Matthias-Stefan/clockgusto/construction/printing/connector_b.stl

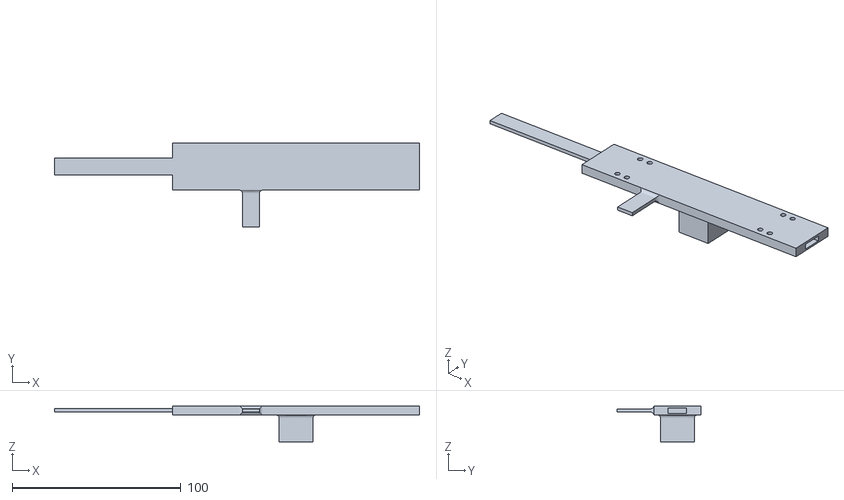
[picture p15: CAD file, 2025-01-12]
construction/printing/connector_b.stl
216.5 x 49.9 x 21.3
