Matthias-Stefan/clockgusto/construction/printing/antenna_nupsi.stl

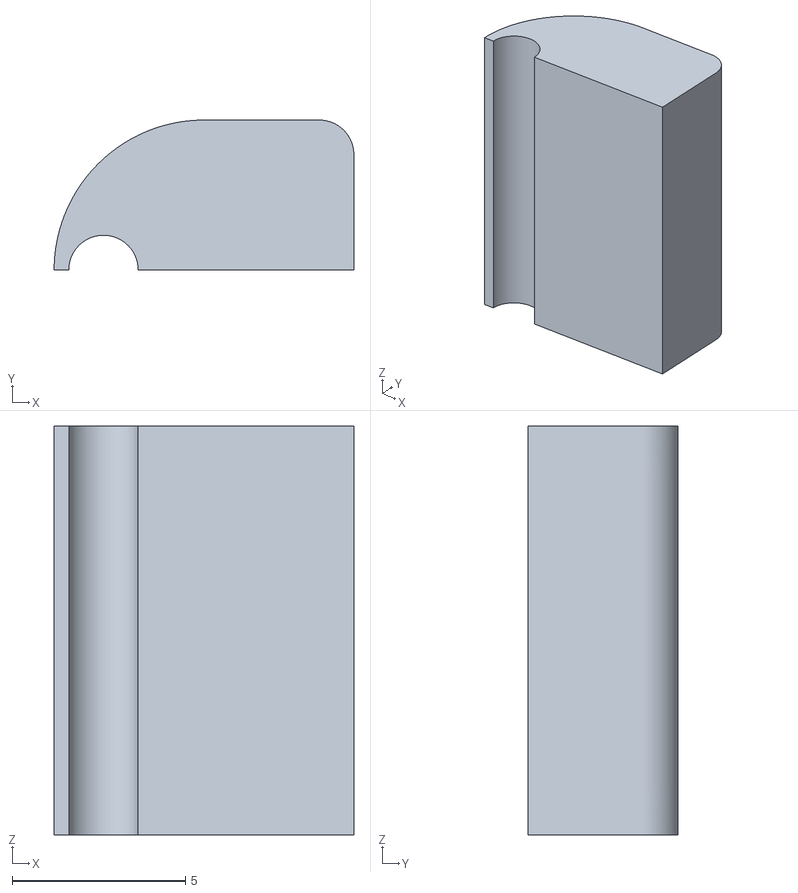
[picture p16: CAD file, 2025-01-12]
construction/printing/antenna_nupsi.stl
8.65 x 4.33 x 11.8
