Matthias-Stefan/clockgusto/construction/printing/nodemcu esp32s_case_bottom.stl

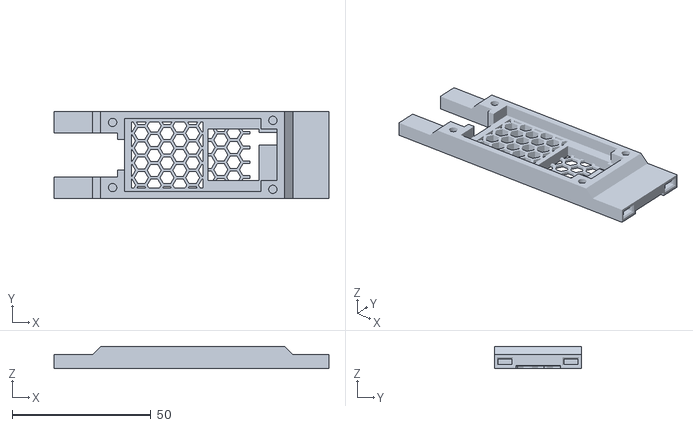
[picture p17: CAD file, 2025-01-12]
construction/printing/nodemcu esp32s_case_bottom.stl
99.0 x 31.2 x 8.00
