Matthias-Stefan/clockgusto/construction/printing/powerbank_case_bottom.stl

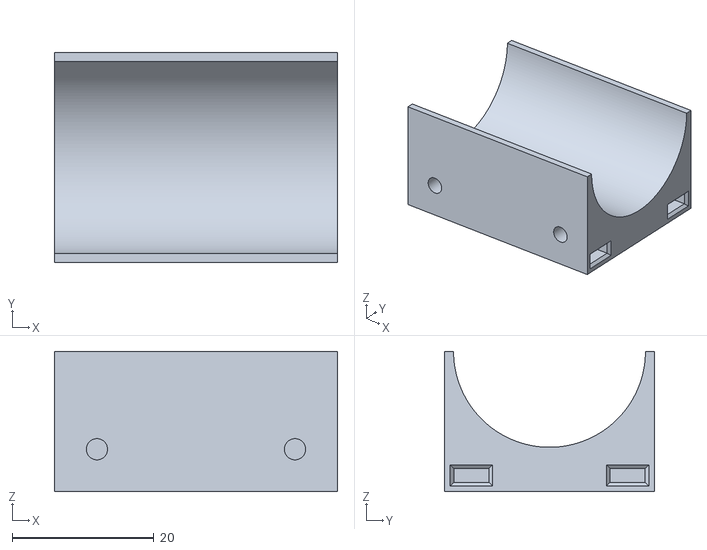
[picture p18: CAD file, 2025-01-12]
construction/printing/powerbank_case_bottom.stl
40.0 x 29.6 x 19.8
