Matthias-Stefan/clockgusto/construction/printing/connector_c.stl

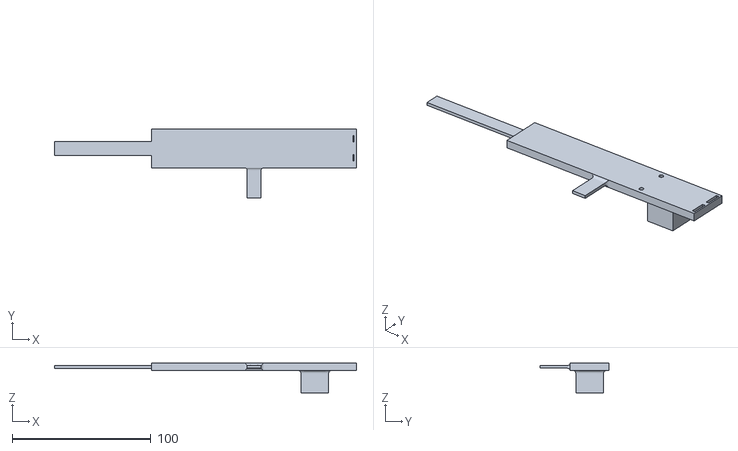
[picture p19: CAD file, 2025-01-12]
construction/printing/connector_c.stl
217.5 x 49.9 x 21.3
