Matthias-Stefan/clockgusto/construction/printing/separator_3x_1.stl

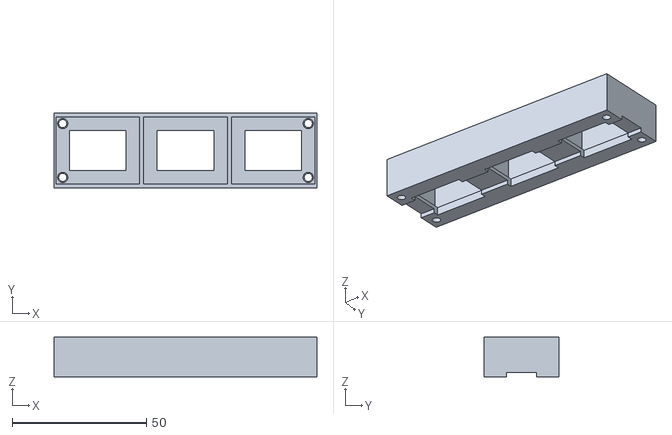
[picture p20: CAD file, 2025-01-12]
construction/printing/separator_3x_1.stl
97.8 x 28.0 x 14.7
