Matthias-Stefan/clockgusto/construction/printing/connector_separator.3mf

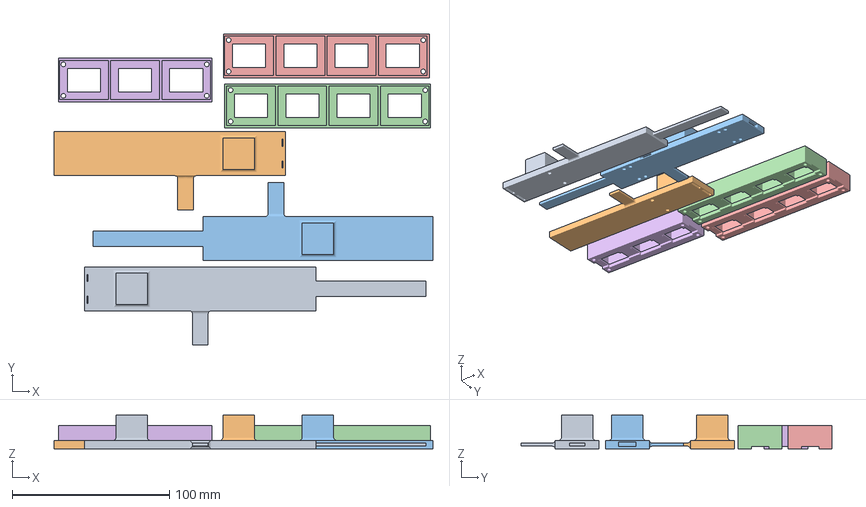
[picture p21: CAD file, 2025-01-12]
construction/printing/connector_separator.3mf
241.3 x 198.3 x 21.3 mm
connector_c.stl
connector_a.stl
connector_b.stl
separator_4x_1.stl
separator_4x_2.stl
separator_3x_1.stl
